srijanpabbi/Mathematical-Alarm-Clock-8085-uP-based/images/DSC_0533_0.jpg

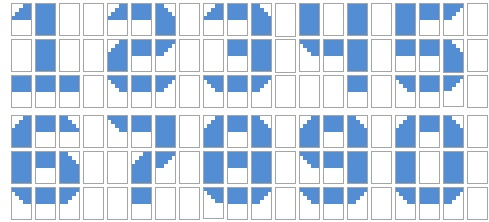
images/DSC_0533_0.jpg
